0firg/Bancada-de-Controle/Lampada_utilizada/WhatsApp Image 2023-12-09 at 13.13.32 (4).jpeg

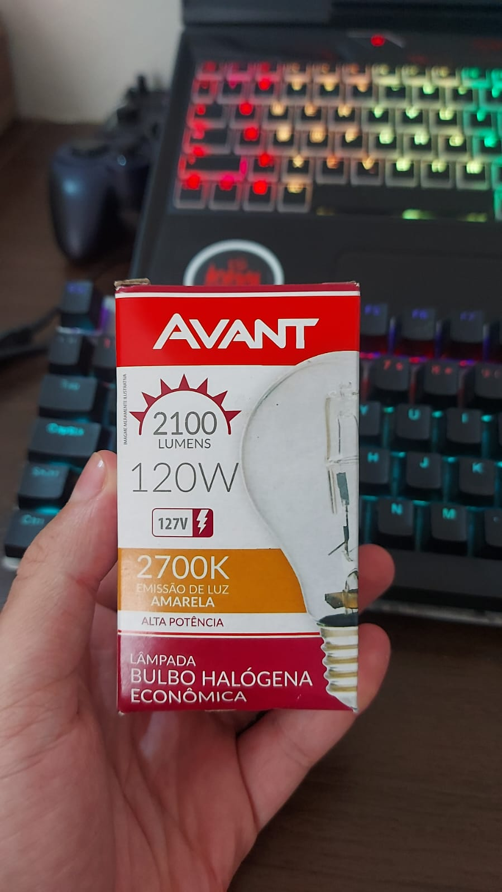
Lampada_utilizada/WhatsApp Image 2023-12-09 at 13.13.32 (4).jpeg
