0firg/Bancada-de-Controle/Arduino_uno/A000066-full-pinout.pdf

PC2 | A2
PC3 | A3

MAXIMUM current per
I/O pin is 20mA
+3.3V pin is 50mA
VIN 6-20V input to the board

GPIO Digital External
Analog External
Main Part
Secondary Part
Internal Component
Other Pins (Reset, System
Control, Debugging)

SKU code: A000066
Full Pinout - Page 1 of 5
Last update: 6 Oct, 2022

CIPO/COPI have previously been
referred to as MISO/MOSI

This work is licensed under
the Creative Commons
Attribution-ShareAlike 4.0
International License. To view a
copy of this license, visit http://
creativecommons.org/licenses/
by-sa/4.0/ or send a letter to
Creative Commons, PO Box 1866,
Mountain View, CA 94042, USA.

# WARNING!

# Advanced Section

# The following information is for advanced use only and may not be officially supported by Arduino software

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

SKU code: A000066
Full Pinout - Page 3 of 5
Last update: 6 Oct, 2022

CIPO/COPI have previously been

Legend:; Power; Power Input; Power Output; Ground; Default; SPI; UART/USART; LED; RGB LED; Other; TOP VIEW; Micro; ATMEGA16U2; Timer; Analog; Interrupt; TCA0/WO0 TCA0/WO1; ICSP-1 ICSP-4 ICSP-3 RESET TX LED RX LED PD0 PD1 ICSP-5; INT[24] INT[25]; AIN[0] AIN[1]; SCK; CIPO UPDI; 1 CIPO 2 +5V 3 SCK 4 COPI 5 RESET 6 GND; ICSP1; ICSP; CIPO; COPI; PCINT[4]; PCINT[5] PCINT[3]; GND; UCAP; VBUS; UVCC; USB D-; USB D+; UGND

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

GPIO Digital External
Analog External
Main Part
Secondary Part

Other SERIAL Communication

SKU code: A000066
Full Pinout - Page 4 of 5
Last update: 6 Oct, 2022

CIPO/COPI have previously been

Legend:; Power; Power Input; Power Output; Ground; LED; RGB LED; Other; TOP VIEW; ATMEGA16U2 PB4 PB6 PB5 PB7; RESET

Cut the solder jumper
to disable auto-reset

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

GPIO Digital External
Analog External
Main Part
Secondary Part

SKU code: A000066
Full Pinout - Page 5 of 5
Last update: 6 Oct, 2022

CIPO/COPI have previously been
